OE9SAU/SAULink9/Node_Case/Node_Case_baseplate/SAULink9_baseplate.png

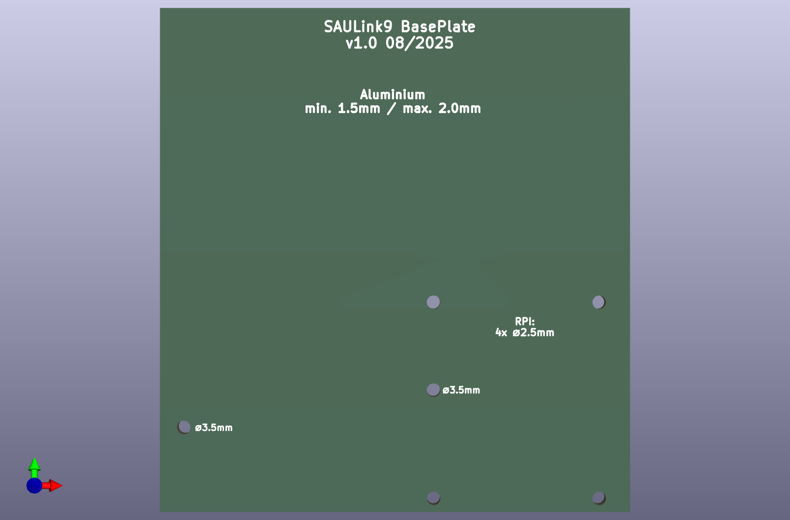
Node_Case/Node_Case_baseplate/SAULink9_baseplate.png
