OE9SAU/SAULink9/Node_Case/Node_Case_cooling/IMG_0264.png

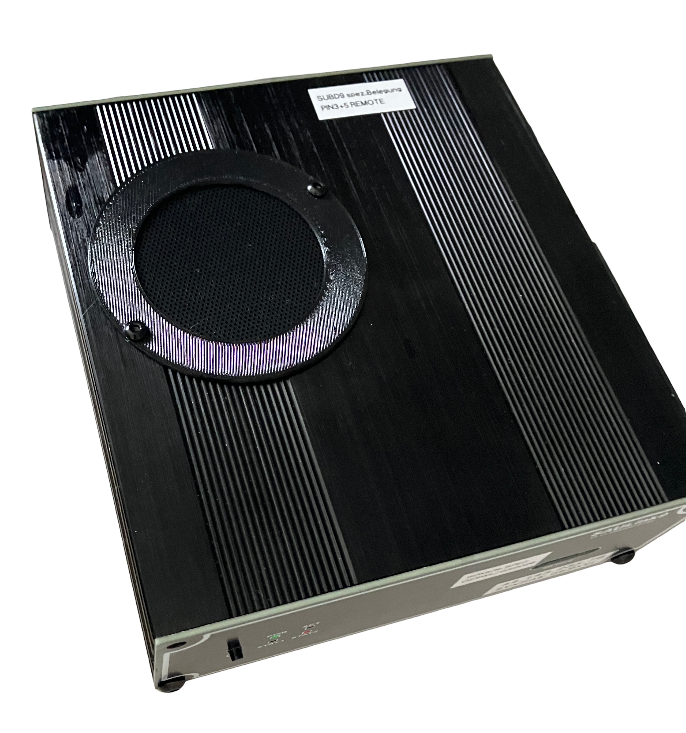
Node_Case/Node_Case_cooling/IMG_0264.png
