OE9SAU/SAULink9/Node_Case/Node_assembly/pics/ATPI.JPG

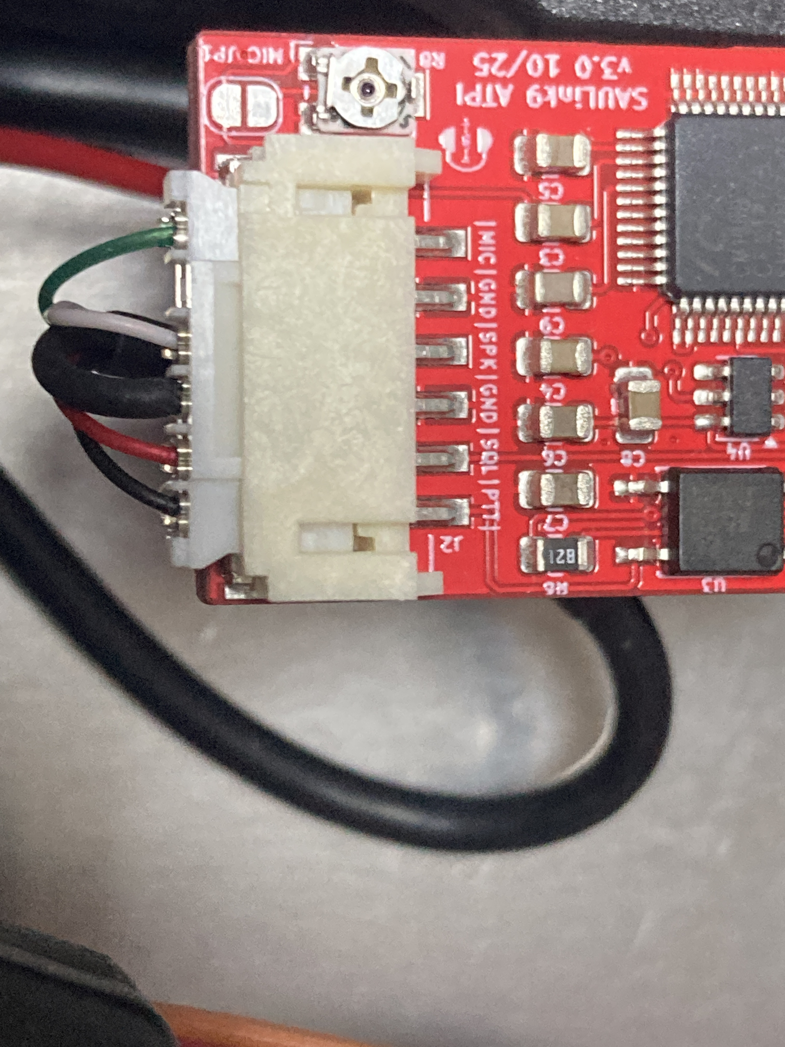
Node_Case/Node_assembly/pics/ATPI.JPG
