OE9SAU/SAULink9/Node_Case/Node_assembly/pics/CONBOARD_GM340_TX.JPG

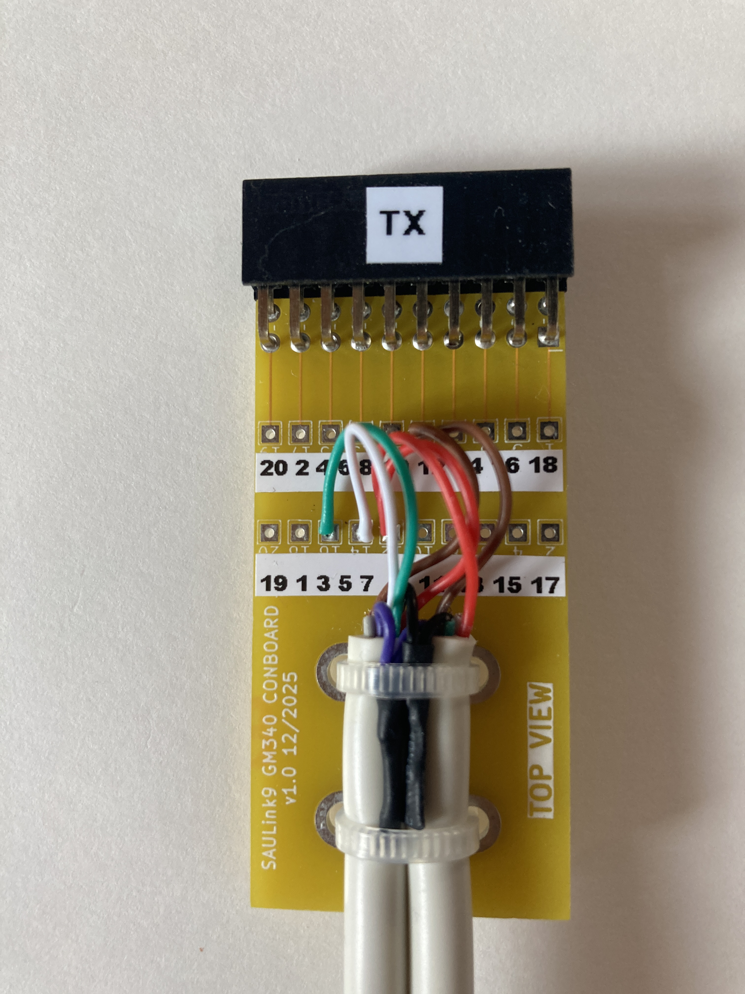
Node_Case/Node_assembly/pics/CONBOARD_GM340_TX.JPG
