OE9SAU/SAULink9/Node_Case/Node_assembly/pics/IMG_1304.JPG

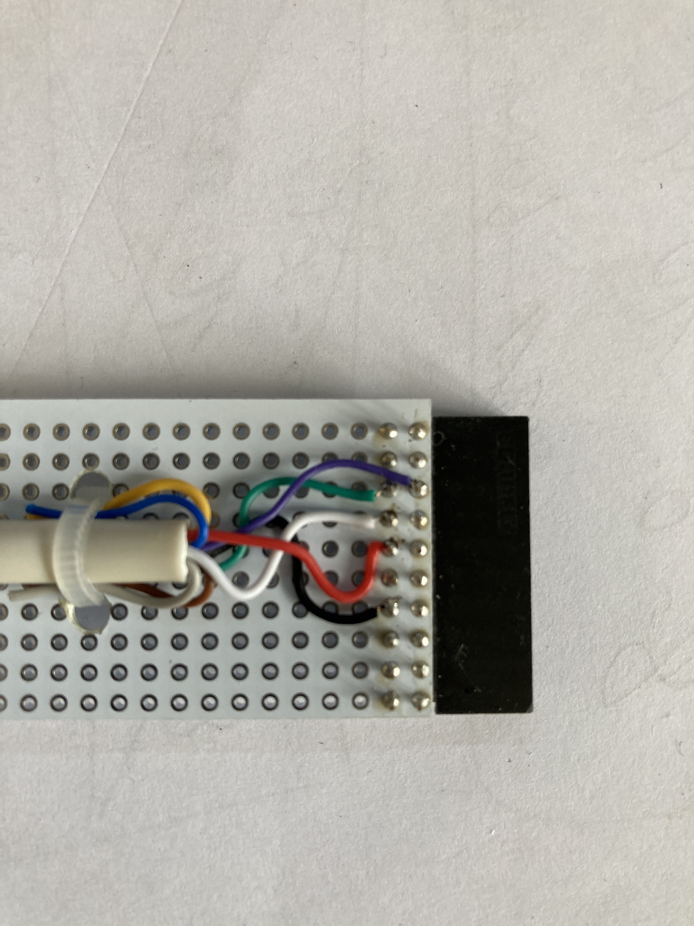
Node_Case/Node_assembly/pics/IMG_1304.JPG
